DccDiyTools/LoconetEsp32/boards/LoconetEsp32Craddle/manual/LoconetEsp32Craddle-bottom.png

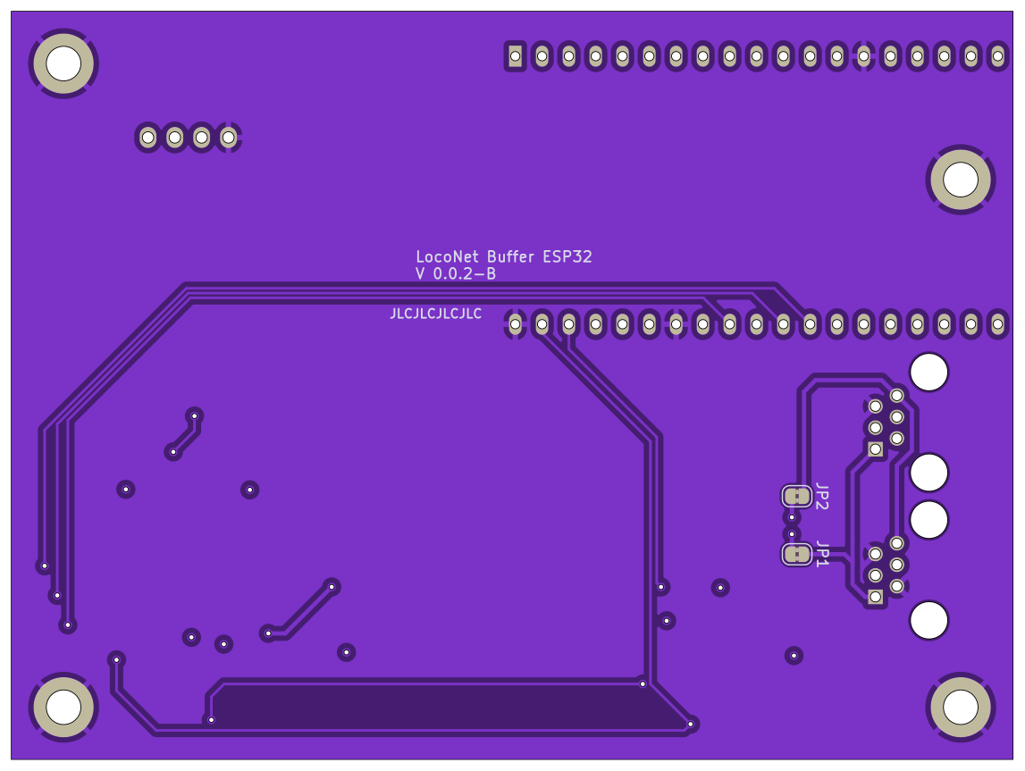
boards/LoconetEsp32Craddle/manual/LoconetEsp32Craddle-bottom.png
