DccDiyTools/LoconetEsp32/boards/LoconetEsp32Craddle/doc/pdf/LoconetEsp32Craddle-F_Fab.pdf

Dcc Diy Tools LED D1 RJ12 RJ12

Size: A4 | Rev: 0.0.1
${KICAD_VERSION} | Id: /1
