DccDiyTools/LoconetEsp32/boards/LoconetEsp32Craddle/doc/pdf/LoconetEsp32Craddle-F_Silkscreen.pdf

Size: A4 | Rev: 0.0.1
${KICAD_VERSION} | Id: /1
