DccDiyTools/LoconetEsp32/boards/LoconetEsp32Craddle/doc/pdf/LoconetEsp32Craddle-In1_Cu.pdf

Size: A4 | Rev: 0.0.1
${KICAD_VERSION} | Id: /1
